linuxboot/flashkeeper/fpga/top.v

/*
 *  PicoSoC - A simple example SoC using PicoRV32
 *
 *  Copyright (C) 2017  Claire Xenia Wolf <claire@yosyshq.com>
 *
 *  Permission to use, copy, modify, and/or distribute this software for any
 *  purpose with or without fee is hereby granted, provided that the above
 *  copyright notice and this permission notice appear in all copies.
 *
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
 */

`ifdef PICOSOC_V
`error "top.v must be read before picosoc.v!"
`endif

`define PICOSOC_MEM ice40up5k_spram

module top (
	output ser_tx,
	input ser_rx,

	output led_n,

	output flash_csb,
	output flash_clk,
	inout  flash_io0,
	inout  flash_io1,

	output hspi_csb,
	output hspi_clk,
	output  hspi_io0,
	input  hspi_io1,
	//inout  hspi_io2, // reserved
	//inout  hspi_io3 // reserved
);
	wire clk;
	parameter integer MEM_WORDS = 32768;

	reg [5:0] reset_cnt = 0;
	wire resetn = &reset_cnt;

	always @(posedge clk) begin
		reset_cnt <= reset_cnt + !resetn;
	end

	wire flash_io0_oe, flash_io0_do, flash_io0_di;
	wire flash_io1_oe, flash_io1_do, flash_io1_di;

	wire hspi_io0_oe, hspi_io0_do, hspi_io0_di;
	wire hspi_io1_oe, hspi_io1_do, hspi_io1_di;

	SB_HFOSC #(.CLKHF_DIV("0b10")) hfosc ( // 0b10 = divide down to 12 MHz
		.CLKHFPU(1'b1),
		.CLKHFEN(1'b1),
		.CLKHF(clk)
	);

	// I/O for onboard SPI flash
	SB_IO #(
		.PIN_TYPE(6'b 1010_01),
		.PULLUP(1'b 0)
	) flash_io_buf [1:0] (
		.PACKAGE_PIN({flash_io1, flash_io0}),
		.OUTPUT_ENABLE({flash_io1_oe, flash_io0_oe}),
		.D_OUT_0({flash_io1_do, flash_io0_do}),
		.D_IN_0({flash_io1_di, flash_io0_di})
	);

    // IO for host SPI
    SB_IO #(
		.PIN_TYPE(6'b 1010_01),
		.PULLUP(1'b 0)
	) hspi_io_buf (
        .PACKAGE_PIN({hspi_io0}),
        .OUTPUT_ENABLE({hspi_io0_oe}),
        .D_OUT_0({hspi_io0_do}),
        .D_IN_0({hspi_io0_di})
    );

	SB_IO #(
		.PIN_TYPE(6'b000001),
		.NEG_TRIGGER(1'b0)
	) mosi_in_driver (
		.PACKAGE_PIN(hspi_io1),
		.D_IN_0(hspi_io1_di)
	);

	wire        iomem_valid;
    wire        iomem_ready;
    wire [3:0]  iomem_wstrb;
    wire [31:0] iomem_addr;
    wire [31:0] iomem_wdata;
    wire [31:0] iomem_rdata;

    // Internal peripheral signals
    wire        gpio_ready;
    reg  [31:0] gpio_rdata;

    reg [31:0] gpio;
    assign led_n = !gpio[0];

    // GPIO Peripheral Logic
    reg gpio_ack;
    always @(posedge clk) begin
        if (!resetn) begin
            gpio <= 0;
            gpio_rdata <= 0;
            gpio_ack <= 0;
        end else begin
            // Acknowledge transaction when valid and addressing GPIO space (0x08xxxxxx)
            gpio_ack <= iomem_valid && !iomem_ready && iomem_addr[31:24] == 8'h08;
            
            if (gpio_ack) begin
                gpio_rdata <= gpio;
                if (iomem_wstrb[0]) gpio[ 7: 0] <= iomem_wdata[ 7: 0];
                if (iomem_wstrb[1]) gpio[15: 8] <= iomem_wdata[15: 8];
                if (iomem_wstrb[2]) gpio[23:16] <= iomem_wdata[23:16];
                if (iomem_wstrb[3]) gpio[31:24] <= iomem_wdata[31:24];
            end
        end
    end
    assign gpio_ready = gpio_ack;

    // Bus Multiplexing (matches PicoSoC internal style)
    assign iomem_ready = gpio_ready;
    assign iomem_rdata = gpio_ready      ? gpio_rdata :
                      32'h0000_0000;

	picosoc #(
		.BARREL_SHIFTER(1),
		.ENABLE_MUL(0),
		.ENABLE_DIV(0),
		.ENABLE_FAST_MUL(1),
		.MEM_WORDS(MEM_WORDS),
		.PROGADDR_RESET(32'h 0600_0000)  // The boot ROM in the EBR (window 0x06000000, see ebrrom.v); it loads the firmware from the SPI flash into the SPRAM and jumps to it
	) soc (
		.clk          (clk         ),
		.resetn       (resetn      ),

		.ser_tx       (ser_tx      ),
		.ser_rx       (ser_rx      ),

		.flash_csb    (flash_csb   ),
		.flash_clk    (flash_clk   ),

		.flash_io0_oe (flash_io0_oe),
		.flash_io1_oe (flash_io1_oe),

		.flash_io0_do (flash_io0_do),
		.flash_io1_do (flash_io1_do),

		.flash_io0_di (flash_io0_di),
		.flash_io1_di (flash_io1_di),

		.hspi_csb    (hspi_csb   ),
		.hspi_clk    (hspi_clk   ),

		.hspi_io0_oe (hspi_io0_oe),
		.hspi_io1_oe (hspi_io1_oe),

		.hspi_io0_do (hspi_io0_do),
		.hspi_io1_do (hspi_io1_do),

		.hspi_io0_di (hspi_io0_di),
		.hspi_io1_di (hspi_io1_di),

		.irq_5        (1'b0        ),
		.irq_6        (1'b0        ),
		.irq_7        (1'b0        ),

		.iomem_valid  (iomem_valid ),
		.iomem_ready  (iomem_ready ),
		.iomem_wstrb  (iomem_wstrb ),
		.iomem_addr   (iomem_addr  ),
		.iomem_wdata  (iomem_wdata ),
		.iomem_rdata  (iomem_rdata )
	);
endmodule
